cliffanet/xdeya-altimeter/arch.hw/v0.5/xdeya-scheme-v0.5.png

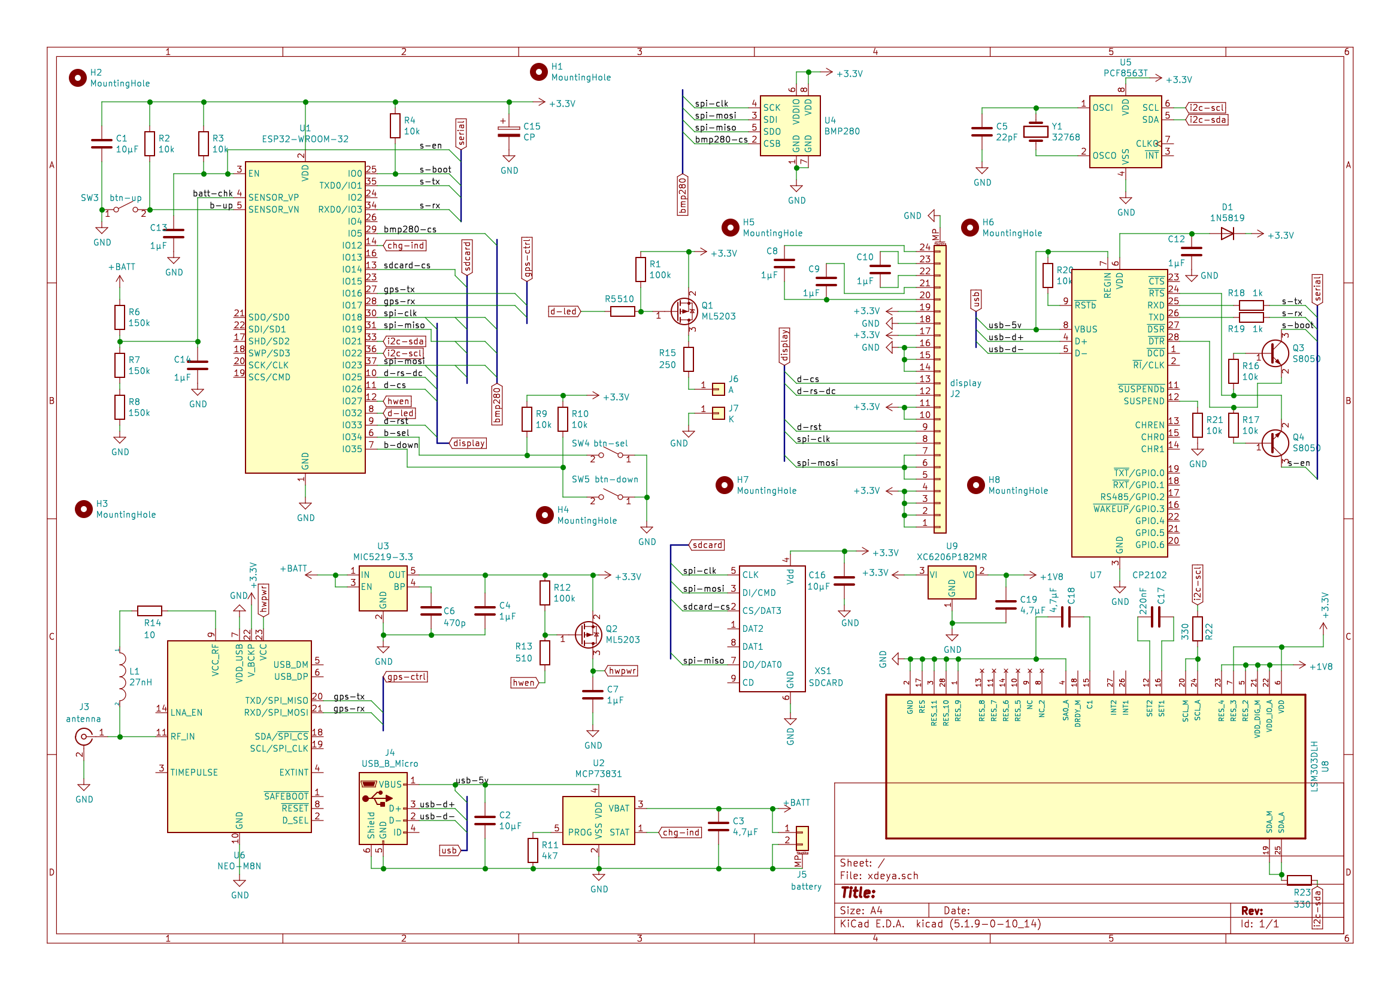
arch.hw/v0.5/xdeya-scheme-v0.5.png
