cliffanet/xdeya-altimeter/doc/models/img/v0.3.i.04.jpg

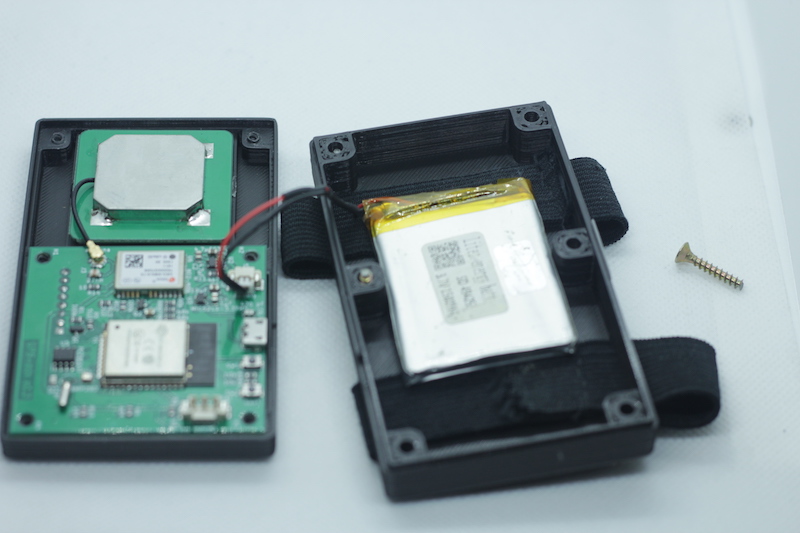
doc/models/img/v0.3.i.04.jpg
