cliffanet/xdeya-altimeter/doc/models/img/v0.3.o.05.jpg

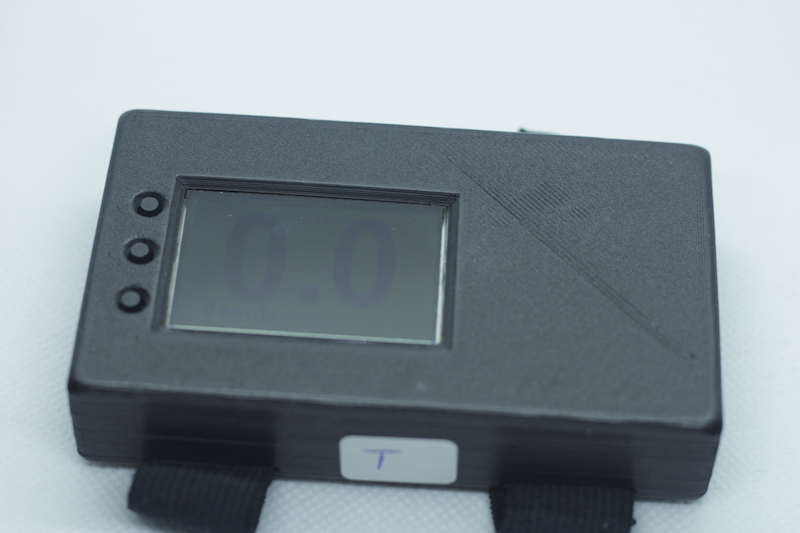
doc/models/img/v0.3.o.05.jpg
