cliffanet/xdeya-altimeter/doc/models/img/v0.4.i.03.jpg

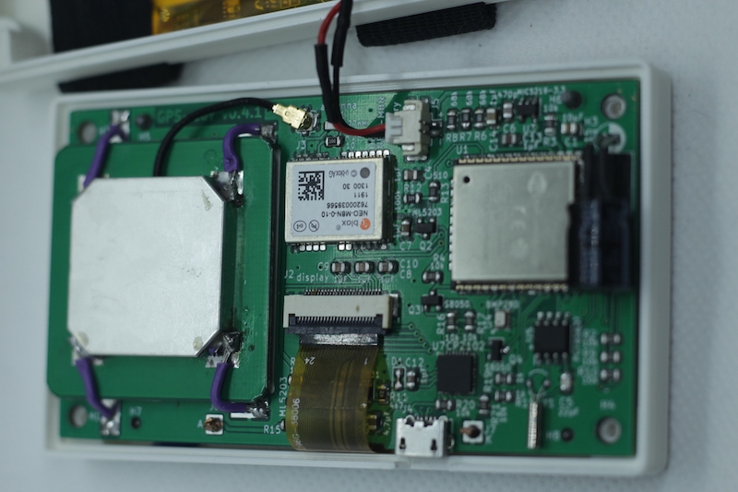
doc/models/img/v0.4.i.03.jpg
