cliffanet/xdeya-altimeter/doc/models/img/v0.4.o.03.jpg

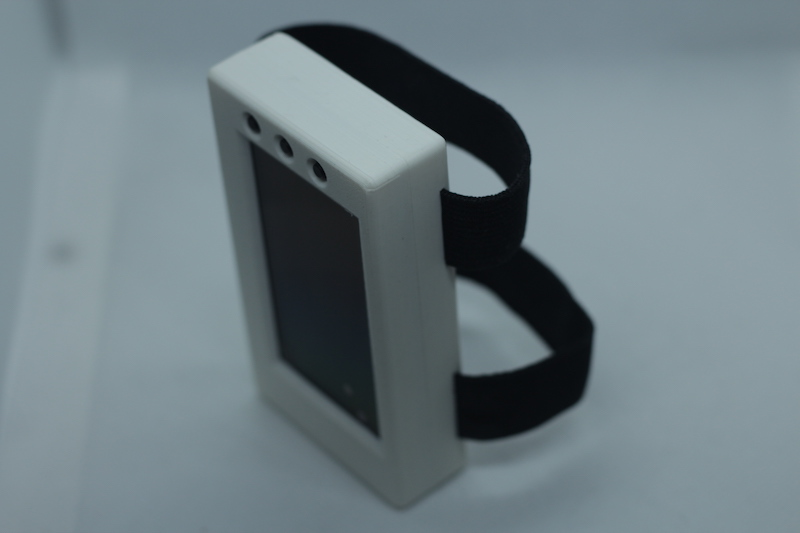
doc/models/img/v0.4.o.03.jpg
