cliffanet/xdeya-altimeter/doc/userman/img/05.horspeed.png

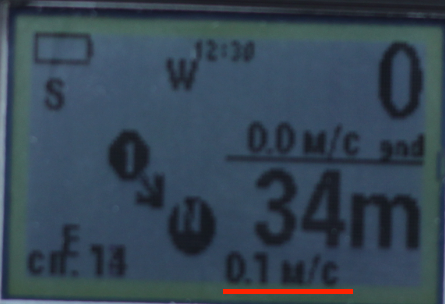
doc/userman/img/05.horspeed.png
