cliffanet/xdeya-altimeter/doc/xdeya.png

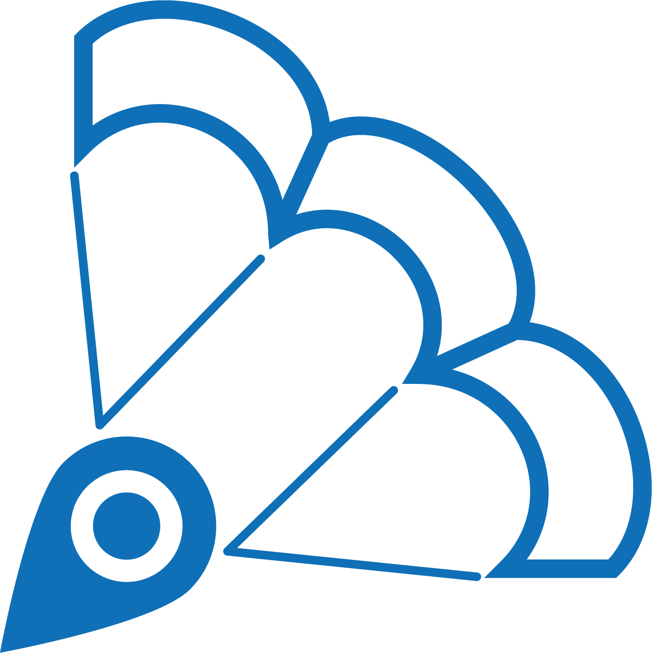
doc/xdeya.png
