cliffanet/xdeya-altimeter/hw/xdeya-scheme-v0.6-t1.png

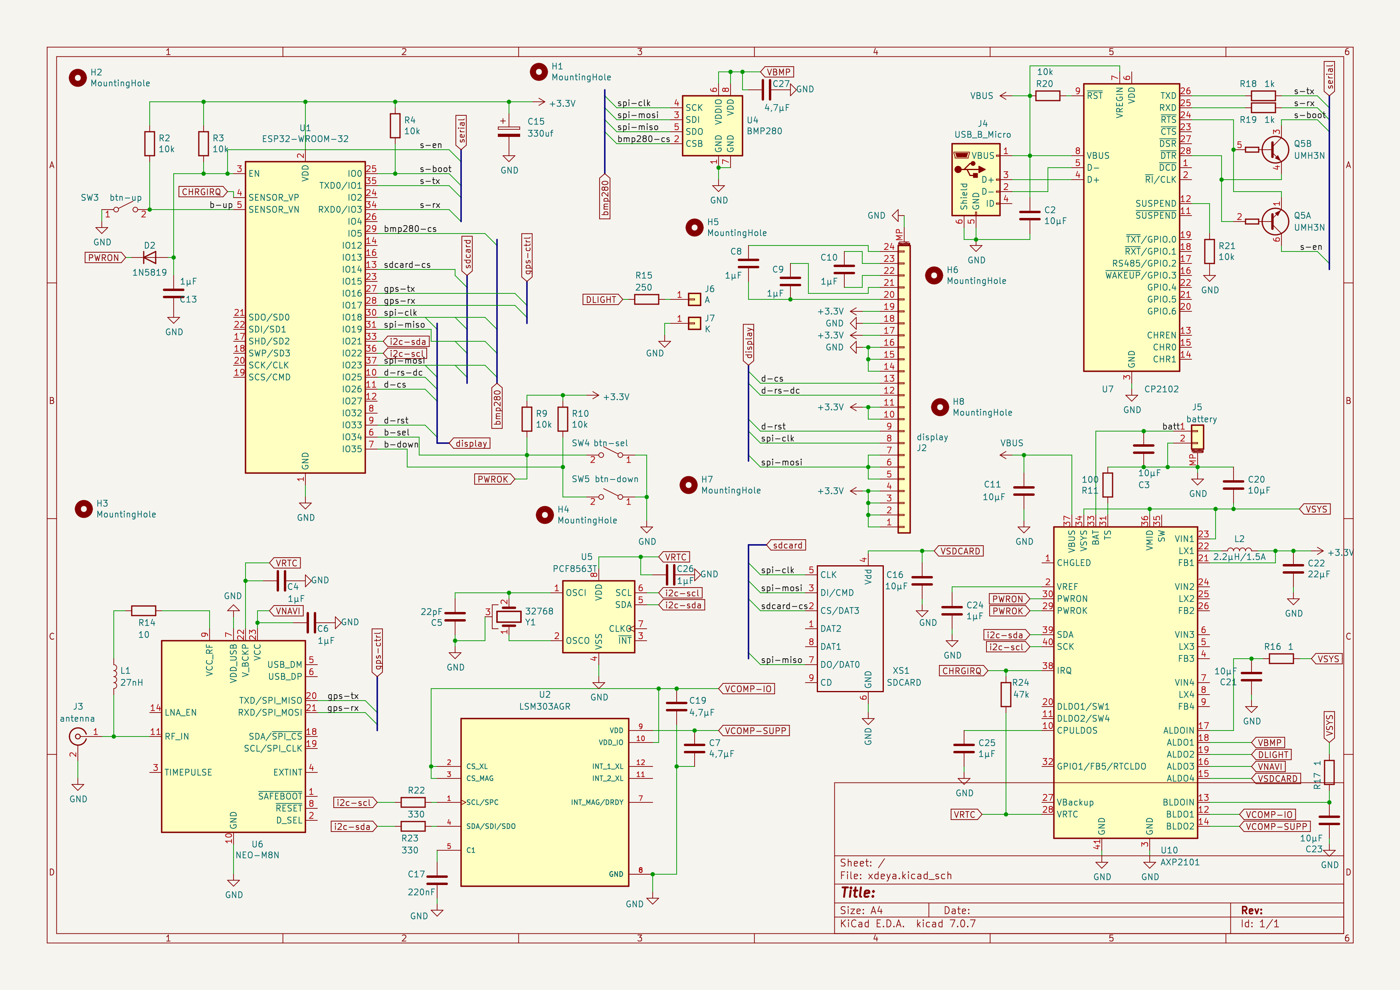
hw/xdeya-scheme-v0.6-t1.png
