cliffanet/xdeya-altimeter/src/view/mainnav.cpp

#include "main.h"

#include "../navi/compass.h"
#include "../navi/proc.h"
#include "../cfg/point.h"
#include "../jump/proc.h"
#include "../jump/track.h"

/* ------------------------------------------------------------------------------------------- *
 *  Навигация
 * ------------------------------------------------------------------------------------------- */
static inline pnt_t pntinit(int cx, int cy, int rx, int ry, double ang) {
    // "PI/2-ang"   - это смещение математического угла до географического
    //                  + преобразование, т.к. математический угол движется против часовой стрелки,
    //                  а географический - по часовой
    // "cy - ..."   - это разница между матиматической осью o-y (снизу вверх) и дисплейной (сверху вниз)
    return {
        static_cast<int>(cx + round(cos(PI/2-ang) * rx)),
        static_cast<int>(cy - round(sin(PI/2-ang) * ry))
    };
}

#define PNT(dr,koef,ang)    pntinit(cx,cy, (h-20+(dr)) * (koef), (ry+(dr)) * (koef), ang)
#define ANG2PNT(dr,koef)    PNT(dr,koef,ang)

#define P2XY                p.x, p.y

#define ARG_COMP_DEF   U8G2 &u8g2, int cx, int cy, int w, int h, int ry
#define ARG_COMP_CALL  u8g2, cx, cy, w, h, ry

/*
static void drawCircleSeg(U8G2 &u8g2, int x, int y, int cx, int cy) {
    u8g2.drawPixel(cx-x, cy-y);
    u8g2.drawPixel(cx-y, cy-x);
    u8g2.drawPixel(cx+x, cy-y);
    u8g2.drawPixel(cx+y, cy-x);
}
*/

static void drawGrid(ARG_COMP_DEF) {
    u8g2.drawDisc(cx, cy, 2);
    
    if (compass().ok)
        u8g2.drawEllipse(cx, cy, h-20, ry, U8G2_DRAW_UPPER_LEFT | U8G2_DRAW_UPPER_RIGHT);
    else
        u8g2.drawEllipse(cx, cy, h-20, ry);
    /*
    return;
    
    int rad = h-20;
    int
        f = 1-rad,
        x = 0,
        y = rad,
        dx = 1,
        dy = (0-rad)*2;
    
    drawCircleSeg(u8g2, x, y, cx, cy);
    
    while (x < y) {
        if (f > 0) {
            y --;
            dy += 2;
            f += dy;
        }
        
        x ++;
        dx += 2;
        f += dx;
        if ((x & 0x3) != 0x3) // для каждого 0, 1, 2, 3 - пропускаем 0, 1 и 2
            continue;
    
        drawCircleSeg(u8g2, x, y, cx, cy);
    }
    */
}

static void drawText(ARG_COMP_DEF) {
    // Шрифт для высоты и расстояния
#if HWVER < 4
    u8g2.setFont(u8g2_font_helvB08_tr);
#else // if HWVER < 4
    u8g2.setFont(u8g2_font_fub20_tf);
#endif
    
    // Высота
    ViewMain::drawAlt(u8g2, 0, u8g2.getAscent());
    
    // Расстояние до точки
    ViewMain::drawNavDist(u8g2, u8g2.getAscent());
    
    // Количество спутников
    ViewMain::drawNavSat(u8g2);
    
    // запись трека
#if HWVER < 4
    u8g2.setFont(u8g2_font_tom_thumb_4x6_mn);
#else // if HWVER < 4
    u8g2.setFont(menuFont);
#endif
    if (trkRunning() && View::isblink())
        u8g2.drawGlyph(0, h-u8g2.getAscent(), 'R');
}

static void drawTxtCourse(ARG_COMP_DEF) {
    auto &gps = gpsInf();
    char s[50];
    #if HWVER < 4
        const int hb = 24;
    #else // if HWVER < 4
        const int hb = 36;
    #endif
    
    if (gps.validLocation() && gps.validPoint() && gps.validHead()) {
        int y = compass().ok ? cy-(hb/5*4) : cy-(hb/2);
        
        u8g2.setDrawColor(0);
        u8g2.drawBox(cx/3, y, cx*2/3-7, hb);
        u8g2.setDrawColor(1);
        
        strcpy_P(s, PTXT(MAIN_NAVSTATE_CRS));
        u8g2.setFont(menuFont);
        y += u8g2.getAscent()+2;
        u8g2.drawTxt(cx-u8g2.getTxtWidth(s)-10, y, s);
        
        sprintf_P(s, PSTR("%d"), gps.headDegI());
        #if HWVER < 4
            u8g2.setFont(u8g2_font_helvB08_tr);
        #else // if HWVER < 4
            u8g2.setFont(u8g2_font_fub20_tf);
        #endif
        y += u8g2.getAscent()+2;
        u8g2.drawStr(cx-u8g2.getTxtWidth(s)-10, y, s);
    }
    
    if (gps.validLocation() && gps.validPoint() && pnt.numValid() && pnt.cur().used) {
        int y = compass().ok ? cy-(hb/5*4) : cy-(hb/2);
        
        u8g2.setDrawColor(0);
        u8g2.drawBox(cx+7, y, cx*2/3-7, hb);
        u8g2.setDrawColor(1);
        
        strcpy_P(s, PTXT(MAIN_NAVSTATE_PNT));
        u8g2.setFont(menuFont);
        y += u8g2.getAscent()+2;
        u8g2.drawTxt(cx+10, y, s);
        
        double ang =
            gpsCourse(
                gps.getLat(),
                gps.getLon(),
                pnt.cur().lat, 
                pnt.cur().lng
            );
        sprintf_P(s, PSTR("%0.0f"), ang);
        #if HWVER < 4
            u8g2.setFont(u8g2_font_helvB08_tr);
        #else // if HWVER < 4
            u8g2.setFont(u8g2_font_fub20_tf);
        #endif
        y += u8g2.getAscent()+2;
        u8g2.drawStr(cx+10, y, s);
    }
}

static void drawPntC(U8G2 &u8g2, const pnt_t &p) {
    u8g2.setDrawColor(0);
    u8g2.drawDisc(P2XY, 8);
    u8g2.setDrawColor(1);
    u8g2.drawDisc(P2XY, 6);
    u8g2.setFont(u8g2_font_helvB08_tr);
    u8g2.setDrawColor(0);
    u8g2.drawGlyph(p.x-2,p.y+4, '0' + pnt.num());
    u8g2.setDrawColor(1);
}

static void drawPoint(ARG_COMP_DEF, double head = 0) {
    auto &gps = gpsInf();
    
    double dist =
        gpsDistance(
            gps.getLat(),
            gps.getLon(),
            pnt.cur().lat, 
            pnt.cur().lng
        );
    
    if (dist < 8) {
        // in point
        drawPntC(u8g2, { cx,cy });
        u8g2.drawCircle(cx,cy, 10);
        u8g2.drawCircle(cx,cy, 15);
        return;
    }
    
    double ang =
        gpsCourse(
            gps.getLat(),
            gps.getLon(),
            pnt.cur().lat, 
            pnt.cur().lng
        ) * DEG_TO_RAD + head;
    
    double koef = dist > 400 ? 1 : static_cast<double>(dist) / 400;
    auto p = ANG2PNT(0, koef);
    if (p.y > h-7) p.y = h-7;
    drawPntC(u8g2, p);
}

static void drawMove(ARG_COMP_DEF, double head = 0) {
    auto &gps = gpsInf();
    double ang = gps.headRad() + head;
    
    double speed = NAV_CM_F(gps.gSpeed);
    
    if (speed < 0.5)
        return;
    /*
    drawMoveArr(ARG_COMP_CALL, 0, head);
    if (speed < 5)
        return;
    drawMoveArr(ARG_COMP_CALL, 1, head);
    if (speed < 15)
        return;
    drawMoveArr(ARG_COMP_CALL, 2, head);
    if (speed < 25)
        return;
    drawMoveArr(ARG_COMP_CALL, 3, head);
    if (speed < 35)
        return;
    drawMoveArr(ARG_COMP_CALL, 4, head);
    */
    
    pnt_t p;
    
    if (speed < 5) {
        u8g2.drawDisc(cx,cy, 3);
        p = ANG2PNT(0, 0.15);
        u8g2.drawLine(P2XY, cx,cy);
    }
    else
    if (speed < 15) {
        u8g2.drawDisc(cx,cy, 4);
        p = ANG2PNT(0, 0.1);
        u8g2.drawDisc(P2XY, 3);
        p = ANG2PNT(0, 0.20);
        u8g2.drawLine(P2XY, cx,cy);
    }
    else
    if (speed < 25) {
        u8g2.drawDisc(cx,cy, 6);
        p = ANG2PNT(0, 0.14);
        u8g2.drawDisc(P2XY, 4);
        p = ANG2PNT(0, 0.23);
        u8g2.drawDisc(P2XY, 3);
        p = ANG2PNT(0, 0.33);
        u8g2.drawLine(P2XY, cx,cy);
    }
    else
    if (speed < 35) {
        u8g2.drawDisc(cx,cy, 9);
        p = ANG2PNT(0, 0.19);
        u8g2.drawDisc(P2XY, 6);
        p = ANG2PNT(0, 0.32);
        u8g2.drawDisc(P2XY, 4);
        p = ANG2PNT(0, 0.41);
        u8g2.drawDisc(P2XY, 3);
        p = ANG2PNT(0, 0.54);
        u8g2.drawLine(P2XY, cx,cy);
    }
    else {
        u8g2.drawDisc(cx,cy, 13);
        p = ANG2PNT(0, 0.25);
        u8g2.drawDisc(P2XY, 9);
        p = ANG2PNT(0, 0.43);
        u8g2.drawDisc(P2XY, 6);
        p = ANG2PNT(0, 0.56);
        u8g2.drawDisc(P2XY, 4);
        p = ANG2PNT(0, 0.66);
        u8g2.drawDisc(P2XY, 3);
        p = ANG2PNT(0, 0.76);
        u8g2.drawLine(P2XY, cx,cy);
    }
}

static void drawNavi(ARG_COMP_DEF, double head = 0) {
    auto &gps = gpsInf();
    
    if (!gps.valid()) {
        u8g2.setFont(u8g2_font_open_iconic_www_4x_t);
        u8g2.drawGlyph(cx-16, compass().ok ? cy+3 : cy+16, 'J');
        return;
    }

    if (!gps.validPoint()) {
        u8g2.setFont(u8g2_font_open_iconic_www_4x_t);
        u8g2.drawGlyph(cx-16,cy+16, 'R');
        return;
    }
    
    if (gps.validLocation() && pnt.numValid() && pnt.cur().used)
        drawPoint(ARG_COMP_CALL, head);
    
    if (gps.validLocation() && gps.validHead() && gps.validSpeed())
        drawMove(ARG_COMP_CALL, head);
}

static void drawCompass(ARG_COMP_DEF, double head = 0) {
    pnt_t p = PNT(6,1,head);
    
    if (p.y > h-7) p.y = h-7;
    u8g2.setDrawColor(0);
    u8g2.drawDisc(p.x, p.y, 7);

    u8g2.setDrawColor(1);
    u8g2.setFont(u8g2_font_helvB08_tr);
    u8g2.drawGlyph(p.x-3, p.y+4, 'N');
    
    drawNavi(ARG_COMP_CALL, head);
}

class ViewMainNav : public ViewMain {
    public:
        void btnSmpl(btn_code_t btn) {
            if (btn != BTN_SEL)
                return;
    
            setViewMain(MODE_MAIN_NAVPATH);
        }
        
        void draw(U8G2 &u8g2) {
            int w = u8g2.getDisplayWidth();
            int h = u8g2.getDisplayHeight();
            int cx = w/2-1,
                cy = compass().ok ?     h-12    :   h/2-1,
                ry = compass().ok ?     h-20    :   h/2-10;
            
            drawGrid(ARG_COMP_CALL);
            
            drawText(ARG_COMP_CALL); // Весь текст пишем в самом начале, чтобы графика рисовалась поверх
            
            drawCompass(ARG_COMP_CALL, compass().head);
            
            if (cfg.d().navtxtcourse)
                drawTxtCourse(ARG_COMP_CALL);
        }
};
static ViewMainNav vNav;
void setViewMainNav() { viewSet(vNav); }
