cliffanet/xdeya-altimeter/src/view/text.en.h

/*
    View: Text lang
*/

#ifndef _view_text_lang_H
#define _view_text_lang_H

#define menuFont        u8g2_font_ncenB08_tr
#define drawTxt         drawStr
#define getTxtWidth     getStrWidth

#define TXT_MENU_EXIT               "> exit"
#define TXT_MENU_HOLD3SEC           "Hold select 3 sec"

#define TXT_MENU_CONFIG_SAVEERROR   "Config save error"

#define TXT_MENU_ON                 "On"
#define TXT_MENU_OFF                "Off"
#define TXT_MENU_YES                "Yes"
#define TXT_MENU_NO                 "No"
#define TXT_MENU_OK                 "OK"
#define TXT_MENU_FAIL               "fail"
#define TXT_MENU_DISABLE            "disable"

#define TXT_MENU_MAINPAGE_NONE      "No change"
#define TXT_MENU_MAINPAGE_LAST      "Last"
#define TXT_MENU_MAINPAGE_ALTNAV    "Nav+Alt"
#define TXT_MENU_MAINPAGE_ALT       "Alti"
#define TXT_MENU_MAINPAGE_NAV       "Navi"
#define TXT_MENU_MAINPAGE_NAVPATH   "Path"

#define TXT_MENU_POINT_CURRENT      "Current"
#define TXT_MENU_POINT_NOTUSED      " (no used)"
#define TXT_MENU_POINT_NOCURR       "[no point]"
#define TXT_MENU_POINT_SAVE         "Save position"
#define TXT_MENU_POINT_NOTSELECT    "Point not selected"
#define TXT_MENU_POINT_NONAV        "NAVI not valid"
#define TXT_MENU_POINT_EEPROMFAIL   "EEPROM fail"
#define TXT_MENU_POINT_SAVED        "Point saved"
#define TXT_MENU_POINT_CLEAR        "Clear"
#define TXT_MENU_POINT_CLEARED      "Point cleared"

#define TXT_MENU_DISPLAY_LIGHT      "Light"
#define TXT_MENU_DISPLAY_CONTRAST   "Contrast"
#define TXT_MENU_DISPLAY_FLIPP180   "Flipped 180"

#define TXT_MENU_GND_MANUALSET      "Manual set"
#define TXT_MENU_GND_MANUALNOTALLOW "Manual not allowed"
#define TXT_MENU_GND_CORRECTED      "GND corrected"
#define TXT_MENU_GND_MANUALALLOW    "Allow mnl set"
#define TXT_MENU_GND_AUTOCORRECT    "Auto correct"
#define TXT_MENU_GND_CORRECTONGND   "On GND"
#define TXT_MENU_GND_ALTCORRECT     "Alt correction"

#define TXT_MENU_ALT_NUMMODE        "Alt numbers"
#define TXT_MENU_ALT_NUMMETER       "m/km"
#define TXT_MENU_ALT_NUMKM          "km"

#define TXT_MENU_AUTOMAIN_FF        "Auto FF-screen"
#define TXT_MENU_AUTOMAIN_CNP       "On CNP"
#define TXT_MENU_AUTOMAIN_LAND      "After Land"
#define TXT_MENU_AUTOMAIN_ONGND     "On GND"
#define TXT_MENU_AUTOMAIN_POWERON   "Power On"

#define TXT_MENU_POWEROFF_FORCE     "Force Off"
#define TXT_MENU_POWEROFF_NOFLY     "No Fly hours"
#define TXT_MENU_POWEROFF_AFTON     "Aft. Pwr-On"
#define TXT_MENU_POWEROFF_HR        "%d hr"

#define TXT_MENU_NAVON_CURRENT      "Current State"
#define TXT_MENU_NAVON_POWERON      "On by Pwr-On"
#define TXT_MENU_NAVON_TRKREC       "On by Track Rec"
#define TXT_MENU_NAVON_TAKEOFF      "On by Takeoff Alt"
#define TXT_MENU_NAVON_OFFLAND      "Off by Landing"

#define TXT_MENU_NAV_GNSS           "GNSS"
#define TXT_MENU_NAV_GNSS_GLONASS   "GLONASS"
#define TXT_MENU_NAV_GNSS_GPS       "GPS"
#define TXT_MENU_NAV_GNSS_GLONGPS   "GLON+GPS"
#define TXT_MENU_NAV_GNSS_ALL       "all"

#define TXT_MENU_NAV_MODEL              "Model"
#define TXT_MENU_NAV_MODEL_PORTABLE     "PORT"
#define TXT_MENU_NAV_MODEL_STATIONARY   "STATION"
#define TXT_MENU_NAV_MODEL_PEDESTRIAN   "PEDES"
#define TXT_MENU_NAV_MODEL_AUTOMOTIVE   "AUTOMO"
#define TXT_MENU_NAV_MODEL_SEA          "SEA"
#define TXT_MENU_NAV_MODEL_AIRBORN_1G   "AIR<1G"
#define TXT_MENU_NAV_MODEL_AIRBORN_2G   "AIR<2G"
#define TXT_MENU_NAV_MODEL_AIRBORN_4G   "AIR<4G"
#define TXT_MENU_NAV_MODEL_WRISTWORN    "WRIST"
#define TXT_MENU_NAV_MODEL_BIKE         "BIKE"

#define TXT_MENU_NAV_FIXMODE        "Fix-Mode"
#define TXT_MENU_NAV_FIXMODE_AUTO   "Auto"
#define TXT_MENU_NAV_FIXMODE_2D     "2D"
#define TXT_MENU_NAV_FIXMODE_3D     "3D"

#define TXT_MENU_BTNDO_UP           "Btn Up"
#define TXT_MENU_BTNDO_DOWN         "Btn Down"
#define TXT_MENU_BTNDO_NO           "no"
#define TXT_MENU_BTNDO_BACKLIGHT    "BackLight"
#define TXT_MENU_BTNDO_NAVTGL       "Navi On/Off"
#define TXT_MENU_BTNDO_TRKREC       "Track rec"
#define TXT_MENU_BTNDO_POWEROFF     "Power Off"

#define TXT_MENU_TRACK_RECORDING    "Recording"
#define TXT_MENU_TRACK_FORCE        "Force"
#define TXT_MENU_TRACK_AUTO         "Auto"
#define TXT_MENU_TRACK_NOREC        "no"
#define TXT_MENU_TRACK_BYALT        "Auto Rec. by Alt"
#define TXT_MENU_TRACK_COUNT        "Count"
#define TXT_MENU_TRACK_AVAIL        "Avail"
#define TXT_MENU_TRACK_AVAILSEC     "%d s"

#define TXT_MENU_TIME_ZONE          "Zone"

#define TXT_MENU_OPTION_DISPLAY     "Display"
#define TXT_MENU_OPTION_GNDCORRECT  "Gnd Correct"
#define TXT_MENU_OPTION_AUTOSCREEN  "Auto Screen-Mode"
#define TXT_MENU_OPTION_AUTOPOWER   "Auto Power-Off"
#define TXT_MENU_OPTION_AUTONAV     "Auto Navi-On"
#define TXT_MENU_OPTION_COMPEN      "Enable Compass"
#define TXT_MENU_OPTION_TXTCOURSE   "Course text"
#define TXT_MENU_OPTION_NAVNOACC    "Accuracy filter"
#define TXT_MENU_OPTION_BTNDO       "Button operation"
#define TXT_MENU_OPTION_TRACK       "Track"
#define TXT_MENU_OPTION_TIME        "Time"

#define TXT_MENU_FW_VERSION         "FW version"
#define TXT_MENU_FW_TYPE            "FW type"
#define TXT_MENU_FW_HWREV           "Hardware rev."
#define TXT_MENU_FW_UPDATETO        "Update to:"
#define TXT_MENU_FW_NOUPD           "-no-"
#define TXT_MENU_FW_SDCARD          "Update from SD-Card"

#define TXT_MENU_SYSNAV_SERIAL      "Direct serial"
#define TXT_MENU_SYSNAV_SATINFO     "Sat-info"
#define TXT_MENU_SYSNAV_VERINFO     "HW version"
#define TXT_MENU_SYSNAV_COLDRST     "Cold restart"
#define TXT_MENU_SYSNAV_RSTFAIL     "Restart fail"
#define TXT_MENU_SYSNAV_RSTOK       "Restart OK"

#define TXT_MENU_TEST_CLOCK         "Clock"
#define TXT_MENU_TEST_BATTERY       "Battery"
#define TXT_MENU_TEST_BATTCHARGE    "Batt charge"
#define TXT_MENU_TEST_PRESSURE      "Pressure"
#define TXT_MENU_TEST_PRESSVAL      "(%0.0fkPa) %s"
#define TXT_MENU_TEST_LIGHT         "Light test"
#define TXT_MENU_TEST_COMPASS       "Compass"
#define TXT_MENU_TEST_COMPVAL       "(%d) %s"
#define TXT_MENU_TEST_NAVDATA       "GPS data"
#define TXT_MENU_TEST_DATADELAY     "(%d ms) %s"
#define TXT_MENU_TEST_NONAVDATA     "no data"
#define TXT_MENU_TEST_NAVRESTART    "Navi power restart"
#define TXT_MENU_TEST_NAVRESTARTED  "Navi restarted"
#define TXT_MENU_TEST_NAVINIT       "Navi init"
#define TXT_MENU_TEST_NAVINITED     "Navi inited"
#define TXT_MENU_TEST_SDCART        "SD-card"

#define TXT_MENU_SYSTEM_RESTART     "Restart system"
#define TXT_MENU_SYSTEM_FACTORYRES  "Factory reset"
#define TXT_MENU_SYSTEM_FORMATROM   "formating eeprom"
#define TXT_MENU_SYSTEM_EEPROMFAIL  "EEPROM fail"
#define TXT_MENU_SYSTEM_CFGRESETED  "Config reseted"
#define TXT_MENU_SYSTEM_FWUPDATE    "FirmWare update"
#define TXT_MENU_SYSTEM_NAVIGATION  "Navigation module"
#define TXT_MENU_SYSTEM_FILES       "Files"
#define TXT_MENU_SYSTEM_HWTEST      "Hardware test"
#define TXT_MENU_SYSTEM_MAGCALIB    "Mag calibrate"

#define TXT_MENU_WIFICLI_NET        "Net"
#define TXT_MENU_WIFICLI_CONNECTED  "Connected"
#define TXT_MENU_WIFICLI_USED       "Used"
#define TXT_MENU_WIFICLI_STOP       "Stop"
#define TXT_MENU_WIFICLI_STOPPED    "Stopped"

#define TXT_MENU_NET_BLUETOOTH      "Bluetooth"
#define TXT_MENU_NET_WIFICLI        "App whith WiFi"
#define TXT_MENU_NET_WIFISERVER     "To server whith WiFi"
#define TXT_NET_AUTH_TITLE          "Network authorization"
#define TXT_NET_AUTH_TEXT1          "Need enter this code"
#define TXT_NET_AUTH_TEXT2          "in application:"
#define TXT_NET_AUTH_WAIT           "Wait time: % 2d:%02d"

#define TXT_MENU_ROOT_NAVPOINT      "NAVI points"
#define TXT_MENU_ROOT_JUMPCOUNT     "Jump count"
#define TXT_MENU_ROOT_LOGBOOK       "LogBook"
#define TXT_MENU_ROOT_OPTIONS       "Options"
#define TXT_MENU_ROOT_SYSTEM        "System"
#define TXT_MENU_ROOT_NETSYNC       "Net Sync"

#define TXT_MENU_ROOT               "Configuration"

#define TXT_SERVER_DNSFAIL          "DNS lookup failed"
#define TXT_SERVER_LOST             "server connect lost"
#define TXT_SERVER_READFAIL         "fail read from server"
#define TXT_SERVER_PROTOFAIL        "recv proto fail"
#define TXT_SERVER_SENDFAIL         "server send fail"
#define TXT_SERVER_SENDTIMEOUT      "server send timeout"

#define TXT_WIFI_CONNECTTONET       "wifi to %s"
#define TXT_WIFI_WEBSYNC            "Web Sync"
#define TXT_WIFI_NET                "WiFi"
#define TXT_WIFI_STATUS_OFF         "WiFi off"
#define TXT_WIFI_STATUS_DISCONNECT  "Disconnected"
#define TXT_WIFI_STATUS_FAIL        "Connect fail"
#define TXT_WIFI_WAITJOIN           "Wait to JOIN"
#define TXT_WIFI_WAIT_SEC           "%d sec"
#define TXT_WIFI_RSSI               "%3d dBm"
#define TXT_WIFI_SEARCHNET          "... searching ..."
#define TXT_WIFI_NEEDPASSWORD       "Password required!"

#define TXT_WIFI_MSG_WIFIINIT       "WiFi initialize..."
#define TXT_WIFI_MSG_WIFICONNECT    "WiFi connecting..."
#define TXT_WIFI_MSG_SRVCONNECT     "Server connecting..."
#define TXT_WIFI_MSG_SRVAUTH        "Server auth..."
#define TXT_WIFI_MSG_SENDCONFIG     "Sending config..."
#define TXT_WIFI_MSG_SENDJUMPCOUNT  "Sending jump count..."
#define TXT_WIFI_MSG_SENDPOINT      "Sending point..."
#define TXT_WIFI_MSG_SENDLOGBOOK    "Sending LogBook..."
#define TXT_WIFI_MSG_SENDTRACK      "Sending Tracks..."
#define TXT_WIFI_MSG_SENDFIN        "Sending fin..."
#define TXT_WIFI_MSG_JOINACCEPT     "join accepted"
#define TXT_WIFI_MSG_USERCANCEL     "Cancel by user"

#define TXT_WIFI_NEXT_HELLO         "wait hello"
#define TXT_WIFI_NEXT_CONFIRM       "Wait server confirm..."
#define TXT_WIFI_NEXT_RCVPASS       "Recv wifi pass"
#define TXT_WIFI_NEXT_RCVFWVER      "Recv FW-versions"
#define TXT_WIFI_NEXT_FWUPDATE      "FW-update"
#define TXT_WIFI_NEXT_FIN           "Wait server fin..."

#define TXT_WIFI_ERR_WIFIINIT       "WiFi init fail"
#define TXT_WIFI_ERR_WIFICONNECT    "WiFi connect fail"
#define TXT_WIFI_ERR_WIFITIMEOUT    "wifi timeout"
#define TXT_WIFI_ERR_TIMEOUT        "timeout"
#define TXT_WIFI_ERR_JOINLOAD       "Can\'t load JOIN-inf"
#define TXT_WIFI_ERR_SENDDATA       "data send fail"
#define TXT_WIFI_ERR_SENDAUTH       "auth send fail"
#define TXT_WIFI_ERR_SENDCONFIG     "send cfg fail"
#define TXT_WIFI_ERR_SENDJUMPCOUNT  "send cmp count fail"
#define TXT_WIFI_ERR_SENDPOINT      "send pnt fail"
#define TXT_WIFI_ERR_SENDLOGBOOK    "send LogBook fail"
#define TXT_WIFI_ERR_SENDTRACK      "send Tracks fail"
#define TXT_WIFI_ERR_SENDFIN        "Finishing send fail"
#define TXT_WIFI_ERR_SERVERCONNECT  "server can't connect"
#define TXT_WIFI_ERR_SRVDISCONNECT  "server disconnected"
#define TXT_WIFI_ERR_RCVDATA        "recv data fail"
#define TXT_WIFI_ERR_RCVCMDUNKNOWN  "recv unknown cmd"
#define TXT_WIFI_ERR_SAVEJOIN       "save fail"
#define TXT_WIFI_ERR_SENDJOIN       "join send fail"
#define TXT_WIFI_ERR_WORKER         "worker run fail"
#define TXT_WIFI_ERR_PASSCLEAR      "WiFi clear Fail"
#define TXT_WIFI_ERR_PASSCREATE     "WiFi create Fail"
#define TXT_WIFI_ERR_PASSADD        "WiFi add Fail"
#define TXT_WIFI_ERR_VERAVAILCLEAR  "Versions clear Fail"
#define TXT_WIFI_ERR_VERAVAILCREATE "Versions create Fail"
#define TXT_WIFI_ERR_VERAVAILADD    "FW-version add Fail"
#define TXT_WIFI_ERR_FWSIZEBIG      "FW-size too big"
#define TXT_WIFI_ERR_FWINIT         "FW-init fail"
#define TXT_WIFI_ERR_FWWRITE        "FW-write fail"
#define TXT_WIFI_ERR_FWFIN          "FW-finish fail"

#define TXT_WIFI_SYNCFINISHED       "Sync finished"

#define TXT_FWSD_TITLE              "FirmWare from SD-card"
#define TXT_FWSD_ERR_FILEOPEN       "File open fail"
#define TXT_FWSD_ERR_FILEREAD       "File read fail"
#define TXT_FWSD_ERR_MD5            "MD5 fail"
#define TXT_FWSD_ERR_FWSIZEBIG      "FW-size too big"
#define TXT_FWSD_ERR_FWINIT         "FW-init fail"
#define TXT_FWSD_ERR_FWWRITE        "FW-write fail"
#define TXT_FWSD_ERR_FWFIN          "FW-finish fail"
#define TXT_FWSD_ERR_CANCEL         "FW Cancel"

#define TXT_BKPSD_ALL               "Backup all to SD-card"
#define TXT_BKPSD_LAST              "Last jump to SD-card"
#define TXT_BKPSD_FINISH            "Copying finished"
#define TXT_BKPSD_ERR_SDINIT        "SD-cadr init fail"
#define TXT_BKPSD_ERR_MKDIR         "Can\'t make dir"
#define TXT_BKPSD_ERR_FILECREATE    "Can\'t create file"
#define TXT_BKPSD_ERR_FILEREAD      "Can\'t read file"
#define TXT_BKPSD_ERR_FILEWRITE     "Can\'t write file"

#define TXT_MCAL_SAVE               "For SAVE -> Long click"
#define TXT_MCAL_SAVED              "Saved!"
#define TXT_MCAL_SIDE180_1          "Flip to"
#define TXT_MCAL_SIDE180_2          "opposite side"
#define TXT_MCAL_MINFRAME_1         "Minimize"
#define TXT_MCAL_MINFRAME_2         "frame!"

#define TXT_LOGBOOK_JUMPNUM         "Jump # %d"
#define TXT_LOGBOOK_ALTEXIT         "Alt"
#define TXT_LOGBOOK_ALTCNP          "Deploy"
#define TXT_LOGBOOK_TIMETOFF        "Takeoff"
#define TXT_LOGBOOK_TIMEFF          "FF time"
#define TXT_LOGBOOK_TIMESEC         "%d s"
#define TXT_LOGBOOK_TIMECNP         "CNP time"

#define TXT_MAIN_VERTSPEED          "%.0f km/h"
#define TXT_MAIN_NAVSTATE_OFF       "off"
#define TXT_MAIN_NAVSTATE_INIT      "init"
#define TXT_MAIN_NAVSTATE_INITFAIL  "fail"
#define TXT_MAIN_NAVSTATE_NODATA    "no data"
#define TXT_MAIN_NAVSTATE_SATCOUNT  "%d"
#define TXT_MAIN_NAVSTATE_CRS       "crs:"
#define TXT_MAIN_NAVSTATE_PNT       "pnt:"

#define TXT_MAIN_VSPEED_MS          "%0.1f m/s"
#define TXT_MAIN_3DSPEED_MS         "%0.1f m/s"

#endif // _view_text_lang_H
