cliffanet/xdeya-altimeter/src/jump/proc.cpp

#include "proc.h"
#include "track.h"
#include "../log.h"
#include "../monlog.h"
#include "../cfg/main.h"
#include "../navi/proc.h"
#include "../view/base.h"   // btnPushed()
#include "../power.h"       // pwrBattRaw()
#include "../clock.h"

#include <Adafruit_BMP280.h>

#if HWVER <= 1
static Adafruit_BMP280 bmp; // hardware Wire
#else
static Adafruit_BMP280 bmp(5); // hardware SPI on IO5
#endif

static AltCalc ac;

static jmp_cur_t logcursor;
static uint32_t logid = 0;
static log_item_t logall[JMP_PRELOG_SIZE] = { { 0 } };

/* ------------------------------------------------------------------------------------------- *
 * Базовые функции
 * ------------------------------------------------------------------------------------------- */

AltCalc & altCalc() {
    return ac;
}

/* ------------------------------------------------------------------------------------------- *
 *  Сбор текущих данных
 * ------------------------------------------------------------------------------------------- */
static void jmpPreLogAdd(uint16_t interval) {
    auto &gps = gpsInf();
    
    logid++;
    auto &li = logall[logcursor.nxt()];
    
    li = {
        tmoffset    : interval,
        flags       : 0,
        state       : 'U',
        direct      : 'U',
        alt         : static_cast<int16_t>(ac.alt() + cfg.d().altcorrect),
        altspeed    : static_cast<int16_t>(ac.speedapp()*100),
        lon         : gps.lon,
        lat         : gps.lat,
        hspeed      : gps.gSpeed,
        heading     : static_cast<int16_t>(gps.headDegI()),
        gpsalt      : static_cast<int16_t>(NAV_MM(gps.hMSL)),
        vspeed      : gps.speed,
        gpsdage     : gpsDataAge(), // тут вместо millis уже используется только 1 байт для хранения, можно пересмотреть формат
        sat         : gps.numSV,
        _           : 0,
#if HWVER > 1
        batval      : pwrBattRaw(),
#else
        batval      : 0,
#endif
        hAcc        : gps.hAcc,
        vAcc        : gps.vAcc,
        sAcc        : gps.sAcc,
        cAcc        : gps.cAcc,
        //tm          : gps.tm,
        millis      : static_cast<uint32_t>(utm() / 1000),
    };
    
    if (gps.valid())
        li.flags |= LI_FLAG_NAV_VALID;
    if (gps.validLocation())
        li.flags |= LI_FLAG_NAV_VLOC;
    if (gps.validVertical())
        li.flags |= LI_FLAG_NAV_VVERT;
    if (gps.validSpeed())
        li.flags |= LI_FLAG_NAV_VSPEED;
    if (gps.validHead())
        li.flags |= LI_FLAG_NAV_VHEAD;
    if (gps.validTime())
        li.flags |= LI_FLAG_NAV_VTIME;
    
    if (btnPushed(BTN_UP))
        li.flags |= LI_FLAG_BTN_UP;
    if (btnPushed(BTN_SEL))
        li.flags |= LI_FLAG_BTN_SEL;
    if (btnPushed(BTN_DOWN))
        li.flags |= LI_FLAG_BTN_DOWN;
    
    switch (ac.state()) {
        case ACST_INIT:         li.state = 'i'; break;
        case ACST_GROUND:       li.state = 'g'; break;
        case ACST_TAKEOFF40:    li.state = 's'; break;
        case ACST_TAKEOFF:      li.state = 't'; break;
        case ACST_FREEFALL:     li.state = 'f'; break;
        case ACST_CANOPY:       li.state = 'c'; break;
        case ACST_LANDING:      li.state = 'l'; break;
    }
    switch (ac.direct()) {
        case ACDIR_INIT:        li.direct = 'i'; break;
        case ACDIR_ERR:         li.direct = 'e'; break;
        case ACDIR_UP:          li.direct = 'u'; break;
        case ACDIR_FLAT:        li.direct = 'f'; break;
        case ACDIR_DOWN:        li.direct = 'd'; break;
    }

    navPathAdd(ac.jmpmode(), gps.validLocation(), gps.lon, gps.lat, gps.headRad());
}

/* ------------------------------------------------------------------------------------------- *
 *  Получение текущего индекса и данных по любому индексу
 * ------------------------------------------------------------------------------------------- */
uint32_t jmpPreId() { return logid; }
uint16_t jmpPreOld(uint32_t prvid) {
    uint32_t old = logid - prvid;
    return 
        old >= JMP_PRELOG_SIZE ?
            JMP_PRELOG_SIZE-1 :
            old;
}
const jmp_cur_t &jmpPreCursor() {
    // вроде уже нигде не используется, только для отладки
    // можно удалять
    // к функциям jmpPreLog и jmpPreInterval обращаемся теперь только через old,
    // который вычисляем через разницу в jmpPreId() или внутри у себя считаем тики
    return logcursor;
}
const log_item_t &jmpPreLog(uint16_t old) {
    return logall[logcursor[old]];
}

uint32_t jmpPreInterval(uint16_t old) {
    uint32_t interval = 0;
    
    if (old > logcursor.size())
        old = logcursor.size();

    for (; old > 0; old--) {
        interval += logall[logcursor[old-1]].tmoffset;
    }
    
    return interval;
}

/* ------------------------------------------------------------------------------------------- *
 *  Текущее давление "у земли", нужно для отслеживания начала подъёма в режиме "сон"
 * ------------------------------------------------------------------------------------------- */
static RTC_DATA_ATTR float _pressgnd = 101325, _altlast = 0;
static RTC_DATA_ATTR int8_t _toffcnt = 0;
bool jmpTakeoffCheck() {
    jmpInit();
    
    float press = bmp.readPressure();
    float alt = press2alt(_pressgnd, press);
    CONSOLE("_pressgnd: %.2f, press: %.2f, alt: %.2f, _altlast: %.2f, _toffcnt: %d", _pressgnd, press, alt, _altlast, _toffcnt);
    
    if (alt > 100) {
        ac.gndset(press);
        CONSOLE("alt: %0.0f", alt);
        return true;
    }
    if (alt > (_altlast + 0.5)) {
        if (_toffcnt < 0)
            _toffcnt = 0;
        _toffcnt ++;
        if (_toffcnt >= 10) {
            CONSOLE("is toff");
            _toffcnt = 0;
            return true;
        }
    }
    else {
        if (_toffcnt > 0)
            _toffcnt --;
        _toffcnt --;
        if (_toffcnt <= -10) {
            CONSOLE("gnd reset");
            _pressgnd = press;
            _toffcnt = 0;
        }
    }
    
    _altlast = alt;
    
    return false;
}

/* ------------------------------------------------------------------------------------------- *
 *  Обработка изменения режима высотомера
 * ------------------------------------------------------------------------------------------- */
static void altState(ac_jmpmode_t prev, ac_jmpmode_t jmpmode) {
    //MONITOR("state: %d / %d (cnt %d, alt %.0f)", prev, jmpmode, ac.jmpcnt(), ac.alt());
    auto tm = tmNow();
    MONITOR("mode(%d/%d) %d -  %d.%02d.%d %d:%02d:%02d", jmpmode, ac.jmpcnt(), ac.alt(), tm.day, tm.mon, tm.year, tm.h, tm.m, tm.s);
    altchartmode(jmpmode, ac.jmpcnt());

    if ((prev == ACJMP_FREEFALL) && cfg.d().dsplautoff) {
        // Восстанавливаем обработчики после принудительного FF-режима
        setViewMain();
    }

    uint32_t jmpcnt = ac.jmpcnt();

    if ((prev <= ACJMP_TAKEOFF) && (jmpmode > ACJMP_TAKEOFF)) {
        // Начало прыга
        // Т.к. прыг по версии altcalc начинается не с самого момента отделения,
        // а с момента, когда вертикальная скорость превысила порог,
        // эта скорость наступает не сразу, а примерно через 3 сек после отделения,
        // Однако, это справедливо только для начала прыга, поэтому это значение прибавляем
        // только из перехода из статичного состояния (prev <= ACJMP_TAKEOFF)
        jmpcnt += 30;
        // для удобства отладки помечаем текущий jmpPreLog
        // флагом LI_FLAG_JMPDECISS - момент принятия решения о начале прыжка
        logall[*logcursor].flags            |= LI_FLAG_JMPDECISS;
        // А момент, который мы считаем отделением - флагом LI_FLAG_JMPBEG
        logall[logcursor[jmpcnt]].flags |= LI_FLAG_JMPBEG;

        // Временно сделаем, чтобы при автозапуске трека, он начинал писать чуть заранее до отделения
        trkStart(TRK_RUNBY_JMPBEG, jmpcnt+50);
    }
    
    switch (jmpmode) {
        case ACJMP_TAKEOFF:
            jmp.toff(ac.jmpcnt() + 50);
            break;
        
        case ACJMP_FREEFALL:
            if (cfg.d().dsplautoff)
                setViewMain(MODE_MAIN_ALT, false);
            
            jmp.beg(jmpcnt);
            break;
        
        case ACJMP_CANOPY:
            setViewMain(cfg.d().dsplcnp, false);
            
            logall[logcursor[jmpcnt]].flags  |= LI_FLAG_JMPCNP;
            jmp.cnp(jmpcnt);
            break;
            
        case ACJMP_NONE:
            if (prev < ACJMP_NONE)
                return;
            
            setViewMain(cfg.d().dsplland);
            
            // Прыг закончился совсем, сохраняем результат
            logall[*logcursor].flags  |= LI_FLAG_JMPEND;
        
            // Сохраняем
            jmp.end();
            
            // Остановка трека, запущенного автоматически
            trkStop(TRK_RUNBY_JMPBEG | TRK_RUNBY_ALT);

            // на земле выключаем gps после включения на заданной высоте
            gpsOff(NAV_PWRBY_ALT);

            // Принудительное отключение gps после приземления
            if (cfg.d().navoffland && gpsPwr())
                gpsOff();
            
            break;
    }

    // перерисовываем путь на странице navpath
    uint32_t old = ac.jmpcnt()+1;
    if (old > JMP_PRELOG_SIZE)
        old = JMP_PRELOG_SIZE;
    for (; old > 0; old--) {
        auto li = jmpPreLog(old-1);
        navPathAdd(jmpmode, (li.flags & LI_FLAG_NAV_VLOC) > 0, li.lon, li.lat, DEGRAD * li.heading);
    }
    
    tmcntReset(TMCNT_NOFLY, jmpmode == ACJMP_NONE);
}

/* ------------------------------------------------------------------------------------------- *
 *  Инициализация
 * ------------------------------------------------------------------------------------------- */
void jmpInit() {
    if (!bmp.begin(BMP280_ADDRESS_ALT)) {   
        CONSOLE("Could not find a valid BMP280 sensor, check wiring!");
    }
    // В режиме sleep у нас постоянно мониторится "давление земли"
    // Используем его при выходе из сна, 
    // особенно, если выход из сна по причине начала подъёма
    if (pwrMode() == PWR_SLEEP)
        ac.gndset(_pressgnd);
}
void jmpStop() {
    bmp.setSampling(Adafruit_BMP280::MODE_SLEEP);
}

/* ------------------------------------------------------------------------------------------- *
 *  Определяем текущее состояние прыга и переключаем по необходимости
 * ------------------------------------------------------------------------------------------- */
void jmpProcess() {
    static uint32_t tck;
    uint32_t interval = utm_diff32(tck, tck) / 1000;
    ac.tick(bmp.readPressure(), interval);
    jmpPreLogAdd(interval);
    _pressgnd = ac.pressgnd();
    _altlast = ac.alt();
    _toffcnt = 0;
    if (ac.state() > ACST_INIT)
        altchartadd(interval, ac.alt(), ac.altapp(), ac.speedapp(), ac.sqdiff());
    
    // Автокорректировка нуля
    if (cfg.d().gndauto &&
        (ac.state() == ACST_GROUND) &&
        (ac.direct() == ACDIR_FLAT) &&
        (ac.dirtm() >= ALT_AUTOGND_INTERVAL)) {
        ac.gndreset();
        ac.dirreset();
        CONSOLE("auto GND reseted");
    }
    
    // Обработка изменения режима высотомера
    static auto jmpmode = ac.jmpmode();
    if (jmpmode != ac.jmpmode())
        altState(jmpmode, ac.jmpmode());
    jmpmode = ac.jmpmode();
    
    if (ac.jmpmode() == ACJMP_TAKEOFF) {
        // автовключение gps на заданной высоте
        if ((cfg.d().navonalt > 0) &&
            (ac.alt() >= cfg.d().navonalt) &&
            !gpsPwr(NAV_PWRBY_ALT))
            gpsOn(NAV_PWRBY_ALT);
    
        // автовключение записи трека на заданной высоте
        if ((cfg.d().trkonalt > 0) &&
            (ac.alt() >= cfg.d().trkonalt) &&
            !trkRunning(TRK_RUNBY_ALT))
            trkStart(TRK_RUNBY_ALT);
    }
}

/* ------------------------------------------------------------------------------------------- *
 *  Принудительный сброс текущего прыга
 * ------------------------------------------------------------------------------------------- */
void jmpReset() {
    if (jmp.state() != LOGJMP_NONE)
        jmp.end();
}
