cliffanet/xdeya-altimeter/src/view/mainalt.cpp

#include "main.h"
#include "info.h"
#include "../jump/proc.h"
#include "../cfg/main.h"
#include "../monlog.h"

class ViewMainAlt : public ViewMain {
    public:
        void btnSmpl(btn_code_t btn) {
            if (btn != BTN_SEL)
                return;
            
#ifdef FWVER_DEBUG
            setViewMainAltChart();
#else
            setViewMain(MODE_MAIN_ALTNAV);
#endif
        }
        
        void draw(U8G2 &u8g2) {
            char s[20];
            auto &ac = altCalc();
    
            drawState(u8g2);
            drawClock(u8g2);
            
            if (ac.state() == ACST_INIT)
                return;
            
            double alt = ac.alt() + cfg.d().altcorrect;
#if HWVER < 4
            u8g2.setFont(u8g2_font_fub49_tn);
            sprintf_P(s, PSTR("%0.1f"), abs(alt / 1000));
            //uint8_t x = 17; // Для немоноширных шрифтов автоцентровка не подходит (прыгает при смене цифр)
            //uint8_t x = (u8g2.getDisplayWidth()-u8g2.getStrWidth(s))/2;
            uint8_t x = (u8g2.getDisplayWidth()-u8g2.getStrWidth(s))-15;
            u8g2.drawStr(x, 52, s);
            if (alt < -30) // чтобы минус не сдвигал цифры, пишем его отдельно
                u8g2.drawGlyph(-5, 48, '-');
#else // if HWVER < 4
            u8g2.setFont(u8g2_font_logisoso62_tn);
            if (cfg.d().altmeter && (alt < 998)) {
                drawAlt(u8g2, -20, 80);
            }
            else {
                sprintf_P(s, PSTR("%0.1f"), abs(alt / 1000));
                //uint8_t x = 17; // Для немоноширных шрифтов автоцентровка не подходит (прыгает при смене цифр)
                //uint8_t x = (u8g2.getDisplayWidth()-u8g2.getStrWidth(s))/2;
                uint8_t x = (u8g2.getDisplayWidth()-u8g2.getStrWidth(s))-45;
                u8g2.drawStr(x, 80, s);
                if (alt < -30) // чтобы минус не сдвигал цифры, пишем его отдельно
                    u8g2.drawGlyph(0, 70, '-');
            }
#endif // if HWVER < 4
            
            switch (ac.direct()) {
                case ACDIR_UP:
                    u8g2.setFont(u8g2_font_open_iconic_arrow_1x_t);
                    u8g2.drawGlyph(0, u8g2.getDisplayHeight()-1, 0x43);
                    break;
                    
                case ACDIR_DOWN:
                    u8g2.setFont(u8g2_font_open_iconic_arrow_1x_t);
                    u8g2.drawGlyph(0, u8g2.getDisplayHeight()-1, 0x40);
                    break;
            }

            u8g2.setFont(menuFont);
            sprintf_P(s, PTXT(MAIN_VERTSPEED), round(abs(ac.speedapp() * 3.6)));
            u8g2.drawTxt(10, u8g2.getDisplayHeight()-1, s);
        }
};
static ViewMainAlt vAlt;
void setViewMainAlt() { viewSet(vAlt); }
