cliffanet/xdeya-altimeter/src/view/text.ru.font.c

/*
    View: Text font
*/

#include "../../def.h"

#if defined(FWVER_LANG) && (FWVER_LANG == 'R')

#include "text.ru.h"

/*
  Fontname: -FreeType-Roboto-Bold-R-Normal--11-80-100-100-P-62-ISO10646-1
  Copyright: Font data copyright Google 2013
  Glyphs: 175/883
  BBX Build Mode: 0
*/
const uint8_t u8g2_font_robotobd_08_tx[2201] U8G2_FONT_SECTION("u8g2_font_robotobd_08_tx") = 
  "\257\0\3\3\4\4\2\4\5\14\15\0\376\10\376\11\376\1y\2\347\4) \5\0\342\4!\7\202\343"
  "\304a(\42\7\63w\5E\22#\21\206\342U$\26\11\225\42\261H\304\222\26\11\1$\20\246\337U"
  "\220\42\212H\207\23\21)D\213\1%\22\210c\306\224\22\252M\302\264HD\24\211\10'\0&\20\207"
  "#\316L\42\213\310f\224\210d\42\22\31'\7\62\367\304$\2(\13\263\33UD\22\321\247X\0)"
  "\16\243\37EH\224$\221\204\42\222\20\0*\14UnUJ\312(\22\212D\0+\12e\347\225LR"
  "\222\251\0,\7\62\333D\5\0-\6\23o\305\0.\6\22\343\204\0/\15\224\36]H\24\13\305\222"
  "b\61\0\60\13\206\243\315H\242\304\213h\4\61\10\204\243\305!\244\17\62\13\205\243\315D\62\222\211\264"
  "\25\63\16\205\243\5%$\13\15\203\243\10\5\0\64\16\206\243\235lD\212HB\22\233P\2\65\16\205"
  "\243\5%\30\244\204\202\243\10\5\0\66\17\206\243\15E\24\21VD\21\21ED\1\67\13\206\243\205Q"
  "&\14j\214\1\70\20\206\243\15E\24\21I(\242\210\210\24\242\0\71\16\206\243\315H\242D\222\24e"
  "\242\21\0:\7b\343\204\34\42;\10\202\333\204\270\22\1<\11U\247\235d\42\34\12=\7\65\353E"
  "\265\0>\12U\247Ep*\231\310\0\77\15\205\243\5%\24\24\251\311!\42\0@\27\252\333\36Q\66"
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
  "\134(\2\4:\13e\343\205\304\302\42\241\10\4;\13f\242ME_B$\1\4<\14gc\206\254"
  "\342r\250D\4\4=\13e\343\205\204\345 \241\10\4>\14f\343\315H\242\304\42\32\1\4\77\11e"
  "\343\305\205\27\1\4@\15\206\333EE\23\213\244\42\24\2\4A\14e\343\315DBS\221L\0\4B"
  "\12e\343EI\246\13\0\4C\20\205\232\205(\22\221D$\63\265\230\10\0\4D\22\270[\236X\321"
  "\242\22Q\241H\230\214b\31\0\4E\14e\242\205DB\222\211L\1\4F\12\206\33\206D\377bT"
  "\4G\12e\343\205\204EBS\4H\20hc\206DB\221P$\24\11Er\30\4I\16\211\333\206"
  "D\377_\16r\200\34 \4J\16g\42\6UJ\223\210$\42\12\0\4K\16hc\206\220h\242H"
  "(\22\223\0\4L\14e\343\205LF\221P,\0\4M\14e\343\315DiF\221L\0\4N\17h"
  "\243\206\204\242b\62Q$\244\11\0\4O\14e\343\215\205\42\241D(\2\0";

#endif // #if defined(FWVER_LANG) && (FWVER_LANG == 'R')
