cliffanet/xdeya-altimeter/src/navi/proc.h

/*
    NAV - processing
*/

#ifndef _gps_H
#define _gps_H

#include "../../def.h"
#include "../clock.h"

#define NAV_PIN_POWER     27

#define _NAV_MPH_PER_KNOT 1.15077945
#define _NAV_MPS_PER_KNOT 0.51444444
#define _NAV_KMPH_PER_KNOT 1.852
#define _NAV_MILES_PER_METER 0.00062137112
#define _NAV_KM_PER_METER 0.001
#define _NAV_FEET_PER_METER 3.2808399

#define NAV_KOEF_LATLON 10000000L
#define NAV_KOEF_DEG    100000L
#define NAV_KOEF_MM     1000L
#define NAV_KOEF_CM     100L

#define NAV_MM(x)       ((x) / NAV_KOEF_MM)
#define NAV_MM_F(x)     NAV_MM(static_cast<double>(x))
#define NAV_CM(x)       ((x) / NAV_KOEF_CM)
#define NAV_CM_F(x)     NAV_CM(static_cast<double>(x))

#define NAV_TICK_INTERVAL       200

#define DEGRAD 0.017453292519943295769236907684886

typedef struct gps_data_s {
	int32_t  lon;      // Longitude                    (deg * 10^7)
	int32_t  lat;      // Latitude                     (deg * 10^7)
	int32_t  hMSL;     // Height above mean sea level  (mm)
	uint32_t hAcc;     // Horizontal accuracy estimate (mm)
	uint32_t vAcc;     // Vertical accuracy estimate   (mm)

	uint8_t  gpsFix;   // NAV fix type
	uint8_t  numSV;    // Number of SVs in solution

	int32_t  velN;     // North velocity               (cm/s)
	int32_t  velE;     // East velocity                (cm/s)
	int32_t  velD;     // Down velocity                (cm/s)
	int32_t  speed;    // 3D speed                     (cm/s)
	int32_t  gSpeed;   // Ground speed                 (cm/s)
	int32_t  heading;  // 2D heading                   (deg * 10^5)
	uint32_t sAcc;     // Speed accuracy estimate      (cm/s)
	uint32_t cAcc;     // Heading accuracy estimate    (deg * 10^5)
    
    tm_t tm;
    bool rcvok;

    const bool disAcc() const;

    inline
    bool valid()            const { return rcvok && (numSV > 0) && (gpsFix == 3); }
    inline
    bool validPoint()       const { return rcvok && ((lon < -2000) || (lon > 2000)) && ((lat < -2000) || (lat > 2000)); }
    inline
    bool validLocation()    const { return valid() && (disAcc() || (hAcc < 30000)); }
    inline
    bool validVertical()    const { return valid() && (disAcc() || (vAcc < 30000)); }
    inline
    bool validSpeed()       const { return validLocation() && (disAcc() || (sAcc < 1000)); }
    inline
    bool validHead()        const { return validLocation() && (disAcc() || (cAcc < 5000000)); }
    inline
    bool validTime()        const { return valid() && (tm.year > 2000); }

    inline
    double getLon()     const { return static_cast<double>(lon) / NAV_KOEF_LATLON; }
    inline
    double getLat()     const { return static_cast<double>(lat) / NAV_KOEF_LATLON; }

    inline
    double headDegF()   const { return static_cast<double>(heading) / NAV_KOEF_DEG; }
    inline
    int    headDegI()   const { return heading / NAV_KOEF_DEG; }
    inline
    double headRad()    const { return headDegF() * DEGRAD; }
    inline
    double headAcc()    const { return static_cast<double>(cAcc) / NAV_KOEF_DEG; }
} gps_data_t;

typedef enum {
    NAV_STATE_OFF = 0,
    NAV_STATE_INIT,
    NAV_STATE_FAIL,
    NAV_STATE_NODATA,
    NAV_STATE_OK
} gps_state_t;

typedef enum {
    NAV_MODEL_PORTABLE = 0,
    NAV_MODEL_STATIONARY = 2,
    NAV_MODEL_PEDESTRIAN,
    NAV_MODEL_AUTOMOTIVE,
    NAV_MODEL_SEA,
    NAV_MODEL_AIRBORN_1G,
    NAV_MODEL_AIRBORN_2G,
    NAV_MODEL_AIRBORN_4G,
    NAV_MODEL_WRISTWORN,
    NAV_MODEL_BIKE,
} nav_model_t;

class UbloxGpsProto;

void naviInit();

const gps_data_t &gpsInf();
UbloxGpsProto * gpsProto();
uint32_t gpsRecv();
uint32_t gpsRecvError();
uint32_t gpsCmdUnknown();
uint8_t gpsDataAge();
gps_state_t gpsState();
void gpsProcess();

bool gpsColdRestart();

bool gpsUpdateCfgGNSS();
bool gpsUpdateCfgModel();

void gpsDirectTgl();
bool gpsDirect();

double gpsDistance(double lat1, double long1, double lat2, double long2);
double gpsCourse(double lat1, double long1, double lat2, double long2);

#define NAV_PWRBY_HAND      0x01
#define NAV_PWRBY_PWRON     0x02
#define NAV_PWRBY_TRKREC    0x04
#define NAV_PWRBY_ALT       0x08
#define NAV_PWRBY_ANY       0xFF

bool gpsPwr(uint8_t by = NAV_PWRBY_ANY);
void gpsOn(uint8_t by = NAV_PWRBY_HAND);
void gpsPwrDown();
void gpsOff(uint8_t by = NAV_PWRBY_ANY);
void gpsRestart();
void gpsPwrTgl();
void gpsRestore();

#endif // _gps_H
