cliffanet/xdeya-altimeter/src/core/filebin.cpp

#include "filebin.h"
#include "cks.h"

#include "FS.h"

/* ------------------------------------------------------------------------------------------- *
 *  FileBin - работа с бинарными файлами
 * ------------------------------------------------------------------------------------------- */
        
bool FileBin::get(uint8_t *data, uint16_t dsz, bool tailnull) {
    uint16_t sz = 0;
    uint8_t bs[2];
    uint8_t cka = 0, ckb = 0;
    
    if (fh.read(bs, 2) != 2)
        return false;
    
    cks8(bs[0], cka, ckb);
    cks8(bs[1], cka, ckb);
    
    sz |= bs[0];
    sz |= bs[1] << 8;
    sz+=2;
    
    uint8_t buf[sz], *b = buf;
    size_t sz1 = fh.read(buf, sz);
    
    if (sz1 != sz)
        return false;
    
    while ((sz > 2) && (dsz > 0)) {
        cks8(*b, cka, ckb);
        *data = *b;
        b++;
        sz--;
        data++;
        dsz--;
    }
    
    while (sz > 2) {
        cks8(*b, cka, ckb);
        b++;
        sz--;
    }
    
    while (tailnull && (dsz > 0)) {
        *data = 0;
        data++;
        dsz--;
    }
    
    if ((b[0] != cka) || (b[1] != ckb))
        return false;
    
    return true;
}

bool FileBin::add(const uint8_t *data, uint16_t dsz) {
    uint16_t sz = dsz + 4;
    uint8_t buf[sz], *b = buf;
    uint8_t cka = 0, ckb = 0;
    
    *b = dsz & 0xff;
    cks8(*b, cka, ckb);
    b++;
    *b = (dsz & 0xff00) >> 8;
    cks8(*b, cka, ckb);
    b++;
    
    while (dsz > 0) {
        cks8(*data, cka, ckb);
        *b = *data;
        b++;
        data++;
        dsz--;
    }
    
    *b = cka;
    b++;
    *b = ckb;
    
    size_t sz1 = fh.write(buf, sz);
    if (sz1 != sz)
        return false;
    
    return true;
}


/* ------------------------------------------------------------------------------------------- *
 *  FileBinNum - работа с бинарными файлами, которые пишуться как лог файлы с суффиксом .N
 * ------------------------------------------------------------------------------------------- */
bool FileBinNum::open(uint8_t n, mode_t mode, bool external) {
    if (m_fname_P == NULL)
        return false;
    
    char fname[30];
    fileName(fname, sizeof(fname), m_fname_P, n);
    
    return FileBin::open(fname, mode, external);
}

size_t FileBinNum::count(bool external) {
    if (m_fname_P == NULL)
        return false;
    
    return fileCount(m_fname_P, external);
}

bool FileBinNum::renum(bool external) {
    if (fh)
        fh.close();
    if (m_fname_P == NULL)
        return false;
    
    return fileRenum(m_fname_P, external);
}

bool FileBinNum::rotate(uint8_t count, bool external) {
    if (fh)
        fh.close();
    if (m_fname_P == NULL)
        return false;
    
    return fileRotate(m_fname_P, count, external);
}

bool FileBinNum::exists(uint8_t n, bool external) {
    if (m_fname_P == NULL)
        return false;
    
    return fileExists(m_fname_P, n, external);
}

bool FileBinNum::remove(uint8_t n, bool external) {
    if (m_fname_P == NULL)
        return false;
    
    return fileRemove(m_fname_P, n, external);
}
