cliffanet/xdeya-altimeter/def.h

/*
    common
*/

#ifndef _def_H
#define _def_H

#define STRINGIFY(x)        #x
#define TOSTRING(x)         STRINGIFY(x)
#define PPCAT_NX(A, B)      A ## B

#define PTXT(s)             PSTR(TXT_ ## s)

#ifndef HWVER
#define HWVER               5
#endif

#if !defined(FWVER_NUM1) && !defined(FWVER_NUM2) && !defined(FWVER_NUM3)
#define FWVER_NUM1          1
#define FWVER_NUM2          0
#define FWVER_NUM3          0
#endif

#ifndef FWVER_LANG
#define FWVER_LANG          'R'
#endif

#if defined(FWVER_DEV) && !defined(FWVER_DEBUG)
#define FWVER_DEBUG
#endif

/* FW version name */
#if defined(FWVER_NUM1) && defined(FWVER_NUM2) && defined(FWVER_NUM3)

#define FWVER_NUM           FWVER_NUM1.FWVER_NUM2.FWVER_NUM3

#ifdef FWVER_DEV
#define FWVER_TYPE_NAME     ".dev"
#define FWVER_TYPE_DSPL     "dev"
#define FWVER_TYPE_CODE     'D'
#elif defined(FWVER_DEBUG)
#define FWVER_TYPE_NAME     ".debug"
#define FWVER_TYPE_DSPL     "debug"
#define FWVER_TYPE_CODE     'd'
#else
#define FWVER_TYPE_NAME     ""
#define FWVER_TYPE_DSPL     "prod"
#define FWVER_TYPE_CODE     'p'
#endif

#if defined(FWVER_LANG) && (FWVER_LANG == 'R')
#define FWVER_LANG_NAME     ".ru"
#else
#define FWVER_LANG_NAME     ".en"
#endif

#define FWVER_NAME          TOSTRING(FWVER_NUM) ".hw" TOSTRING(HWVER) FWVER_TYPE_NAME FWVER_LANG_NAME
#define FWVER_FILENAME      "xdeya.v" FWVER_NAME

#endif

#if HWVER < 3
#define USE4BUTTON          1
#endif

#if HWVER >= 5
#define USE_SDCARD          1
#endif

#define PI 3.1415926535897932384626433832795

#define WIFIPASS_FILE   "wifi.txt"
#define VERAVAIL_FILE   "veravail.txt"

#define WIFI_PASS_DEFAULT   "z12344321"

#endif // _def_H
