cliffanet/xdeya-altimeter/src/view/menu.h

/*
    View: Menu
*/

#ifndef _view_menu_H
#define _view_menu_H

#include "base.h"

#if HWVER < 4
#define MENU_STR_COUNT  5
#else
#define MENU_STR_COUNT  8
#endif

#if defined(FWVER_LANG) && (FWVER_LANG == 'R')
#define MENUSZ_NAME 96
#define MENUSZ_VAL 32
#else
#define MENUSZ_NAME 48
#define MENUSZ_VAL 16
#endif

#define MENU_TIMEOUT    15000


class ViewMenu : public View {
    public:
        typedef struct {
            char name[MENUSZ_NAME] = { '\0' };
            char val[MENUSZ_VAL] = { '\0' };
        } line_t;

        typedef enum {
            EXIT_NONE,
            EXIT_TOP,
            EXIT_BOTTOM,
        } exit_t;

        ViewMenu(uint16_t _sz, exit_t _exit = EXIT_TOP);
        ViewMenu(exit_t _exit = EXIT_TOP) : ViewMenu(0, _exit) {};
        
        void setSize(uint16_t _sz);
        virtual
        void setTitle(const char *_title = NULL);
        virtual
        void restore() {}
        
        // детектор, является ли указанный пункт меню "выходом"
        bool isExit(int16_t i) { return ((elexit == EXIT_TOP) && (i == 0)) || ((elexit == EXIT_BOTTOM) && (i+1 >= sz)); }

        virtual     // этот метод обновляет строку в потомке
        void getStr(line_t &str, int16_t i) { };
        virtual     // Возвращает PSTR текущего выделенного пункта меню, чтобы его использовать как title для подменю
        const char * getSelName() { return NULL; };
        virtual     // указывает, надо ли моргать текущему значению (режим редактирования)
        bool valFlash() { return false; }
        
        void setTop(int16_t i);  // установка индекса самого верхнего элемента (когда переместились курсором за пределы экрана)
        void setSel(int16_t i); // установка выбранного элемента
        
        void btnSmpl(btn_code_t btn);
        
        void draw(U8G2 &u8g2);
        
        int16_t sel() const { return elexit == EXIT_TOP ? isel-1 : isel; }
        int16_t size() const { return (elexit == EXIT_NONE) || (sz <= 0) ? sz : sz-1; }
    
    protected:
        int16_t itop = 0, isel = 0, sz = 0;
        exit_t elexit;
        const char *titlep = NULL;
};

void _menuAdd(ViewMenu *menu);

template<typename T, typename... _Args>
T* menuOpen(_Args&&... __args) {
    auto m = new T(__args...);
    _menuAdd(m);
    return m;
}

ViewMenu *menuTop();        // просто возвращает текущее меню
ViewMenu *menuPrev();       // переключает на предыдущее меню, текущее уничтожается
ViewMenu *menuRestore();    // перевключает текущее меню (если в нём было сделано viewSet() без menuClear())
void menuClear();
        
// Запоминаем текст сообщения и сколько тактов отображения показывать
void menuFlashP(const char *txt, int16_t count = 20);
// Стандартное сообщение о том, что для данной процедуры нужно удерживать среднюю кнопку три секунды
void menuFlashHold();
void menuFlashClear();

void setViewMenu();

#endif // _view_menu_H
